gdgzdar/Laser-harp/app/images/instruments/glow.png

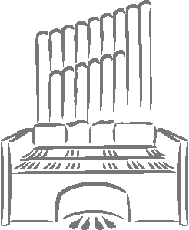
app/images/instruments/glow.png
