gdgzdar/Laser-harp/app/images/instruments/steal.png

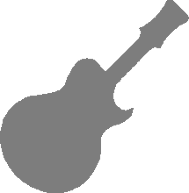
app/images/instruments/steal.png
