gdgzdar/Laser-harp/app/images/instruments/violin.png

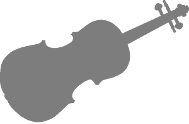
app/images/instruments/violin.png
