gdgzdar/Laser-harp/app/images/notes/empty.png

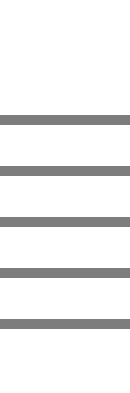
app/images/notes/empty.png
