gdgzdar/Laser-harp/app/images/notes/first-overline.png

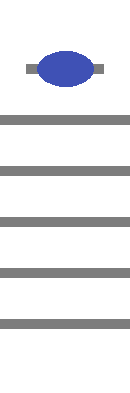
app/images/notes/first-overline.png
