gdgzdar/Laser-harp/app/images/notes/first-subline.png

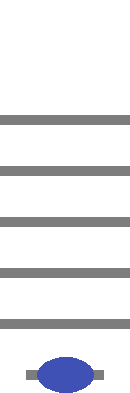
app/images/notes/first-subline.png
