gdgzdar/Laser-harp/app/images/notes/fourth-space-bass.png

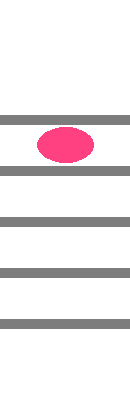
app/images/notes/fourth-space-bass.png
