gdgzdar/Laser-harp/app/images/notes/second-overline.png

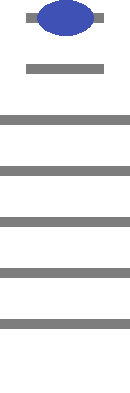
app/images/notes/second-overline.png
