gdgzdar/Laser-harp/app/images/notes/second-space-bass.png

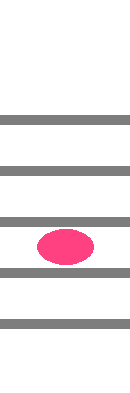
app/images/notes/second-space-bass.png
