gdgzdar/Laser-harp/app/images/notes/third-space-bass.png

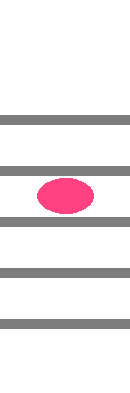
app/images/notes/third-space-bass.png
