gdgzdar/Laser-harp/app/opeal-sound.py

# using Pyglet
from openal import al
from openal import alc
# using PyAL
##from openal import al, alc

# imports for sound loading and wait during example
import wave
import time
import sys
import os


class Example(object):
    def __init__(self, path_to_file, i):
        # load listener
        self.listener = listener()
        # initialize sound
        self.sound = Load_sound(path_to_file)
        # load sound player
        self.player = Player(i)

        # set listener position
        self.listener.position = (320, 240, 0)
        # set player position
        self.player.position = (0, 240, 0)

        # load sound into player
        self.player.add(self.sound)
        # enable loop sound so it plays forever
        # set rolloff factor
        self.player.rolloff = 0.01
        # play sound
        self.player.play()

        # stop player

    #        self.player.stop()

    # clean up resources
    # self.player.delete()
    # self.sound.delete()
    # self.listener.delete()


# load a listener to load and play sounds.
class listener(object):
    def __init__(self):
        # load device/context/listener
        self.device = alc.alcOpenDevice(None)
        self.context = alc.alcCreateContext(self.device, None)
        alc.alcMakeContextCurrent(self.context)

    # set player position
    def _set_position(self, pos):
        self._position = pos
        x, y, z = map(int, pos)
        al.alListener3f(al.AL_POSITION, x, y, z)

    def _get_position(self):
        return self._position

    # delete current listener
    def delete(self):
        alc.alcDestroyContext(self.context)
        alc.alcCloseDevice(self.device)

    position = property(_get_position, _set_position, doc="""get/set position""")


# load and store a wav file into an openal buffer
class Load_sound(object):
    def __init__(self, filename):
        self.name = filename
        # load/set wav file
        if len(sys.argv) < 2:
            print ("Usage: %s wavefile" % os.path.basename(sys.argv[0]))
            print ("    Using an example wav file...")
            dirname = os.path.dirname(os.path.realpath(__file__))
            fname = os.path.join(dirname, filename)
        else:
            fname = sys.argv[1]

        wavefp = wave.open(fname)
        channels = wavefp.getnchannels()
        bitrate = wavefp.getsampwidth() * 8
        samplerate = wavefp.getframerate()
        wavbuf = wavefp.readframes(wavefp.getnframes())
        self.duration = (len(wavbuf) / float(samplerate)) / 2
        self.length = len(wavbuf)
        formatmap = {
            (1, 8): al.AL_FORMAT_MONO8,
            (2, 8): al.AL_FORMAT_STEREO8,
            (1, 16): al.AL_FORMAT_MONO16,
            (2, 16): al.AL_FORMAT_STEREO16,
        }
        alformat = formatmap[(channels, bitrate)]

        self.buf = al.ALuint(0)
        al.alGenBuffers(1, self.buf)
        # allocate buffer space to: buffer, format, data, len(data), and samplerate
        al.alBufferData(self.buf, alformat, wavbuf, len(wavbuf), samplerate)

    # delete loaded sound
    def delete(self):
        al.alDeleteBuffers(1, self.buf)


# load sound buffers into an openal source player to play them
class Player(object):
    # load default settings
    def __init__(self, i):
        # load source player
        self.source = al.ALuint(i)
        al.alGenSources(1, self.source)
        # disable rolloff factor by default
        al.alSourcef(self.source, al.AL_ROLLOFF_FACTOR, 0)
        # disable source relative by default
        al.alSourcei(self.source, al.AL_SOURCE_RELATIVE, 0)
        # capture player state buffer
        self.state = al.ALint(i)
        # set internal variable tracking
        self._volume = 1.0
        self._pitch = 1.0
        self._position = [0, 0, 0]
        self._rolloff = 1.0
        self._loop = False
        self.queue = []

    # set rolloff factor, determines volume based on distance from listener
    def _set_rolloff(self, value):
        self._rolloff = value
        al.alSourcef(self.source, al.AL_ROLLOFF_FACTOR, value)

    def _get_rolloff(self):
        return self._rolloff

    # set whether looping or not - true/false 1/0
    def _set_loop(self, lo):
        self._loop = lo
        al.alSourcei(self.source, al.AL_LOOPING, lo)

    def _get_loop(self):
        return self._loop

    # set player position
    def _set_position(self, pos):
        self._position = pos
        x, y, z = map(int, pos)
        al.alSource3f(self.source, al.AL_POSITION, x, y, z)

    def _get_position(self):
        return self._position

    # set pitch - 1.5-0.5 float range only
    def _set_pitch(self, pit):
        self._pitch = pit
        al.alSourcef(self.source, al.AL_PITCH, pit)

    def _get_pitch(self):
        return self._pitch

    # set volume - 1.0 float range only
    def _set_volume(self, vol):
        self._volume = vol
        al.alSourcef(self.source, al.AL_GAIN, vol)

    def _get_volume(self):
        return self._volume

    # queue a sound buffer
    def add(self, sound):
        al.alSourceQueueBuffers(self.source, 1, sound.buf)  # self.buf
        self.queue.append(sound)

    # remove a sound from the queue (detach & unqueue to properly remove)
    def remove(self):
        if len(self.queue) > 0:
            al.alSourceUnqueueBuffers(self.source, 1, self.queue[0].buf)  # self.buf
            al.alSourcei(self.source, al.AL_BUFFER, 0)
            self.queue.pop(0)

            # play sound source

    def play(self):
        al.alSourcePlay(self.source)

    # get current playing state
    def playing(self):
        al.alGetSourcei(self.source, al.AL_SOURCE_STATE, self.state)
        if self.state.value == al.AL_PLAYING:
            return True
        else:
            return False

            # stop playing sound

    def stop(self):
        al.alSourceStop(self.source)

    # rewind player
    def rewind(self):
        al.alSourceRewind(self.source)

    # pause player
    def pause(self):
        al.alSourcePause(self.source)

    # delete sound source
    def delete(self):
        al.alDeleteSources(1, self.source)

    # Go straight to a set point in the sound file
    def _set_seek(self, offset):  # float 0.0-1.0
        al.alSourcei(self.source, al.AL_BYTE_OFFSET, int(self.queue[0].length * offset))

    # returns current buffer length position (IE: 21000), so divide by the buffers self.length
    def _get_seek(self):  # returns float 0.0-1.0
        al.alGetSourcei(self.source, al.AL_BYTE_OFFSET, self.state)
        return float(self.state.value) / float(self.queue[0].length)

    rolloff = property(_get_rolloff, _set_rolloff, doc="""get/set rolloff factor""")
    volume = property(_get_volume, _set_volume, doc="""get/set volume""")
    pitch = property(_get_pitch, _set_pitch, doc="""get/set pitch""")
    loop = property(_get_loop, _set_loop, doc="""get/set loop state""")
    position = property(_get_position, _set_position, doc="""get/set position""")
    seek = property(_get_seek, _set_seek, doc="""get/set the current play position""")
