gdgzdar/Laser-harp/app/StartUpDialog.py

from kivy.uix.dropdown import DropDown
from kivy.uix.button import Button
from kivy.base import runTouchApp
from audio import Reader

# create a dropdown with 10 buttons
dropdown = DropDown()

list_of_ports = Reader.get_available_ports()


for i in range(len(list_of_ports)):
    btn = Button(text= list_of_ports[i], size_hint_y=None, height=44)
    btn.bind(on_release=lambda btn: dropdown.select(btn.text))

    # then add the button inside the dropdown
    dropdown.add_widget(btn)

# create a big main button
mainbutton = Button(text='Select port', size_hint=(None, None))

# show the dropdown menu when the main button is released
# note: all the bind() calls pass the instance of the caller (here, the
# mainbutton instance) as the first argument of the callback (here,
# dropdown.open.).
mainbutton.bind(on_release=dropdown.open)

# one last thing, listen for the selection in the dropdown list and
# assign the data to the button text.
dropdown.bind(on_select=lambda instance, x: setattr(mainbutton, 'text', x))

runTouchApp(mainbutton)
